TimoWey/Belimo_RoomUnit_ESP32-C3/3D-Design/Assembly_Top_View.png

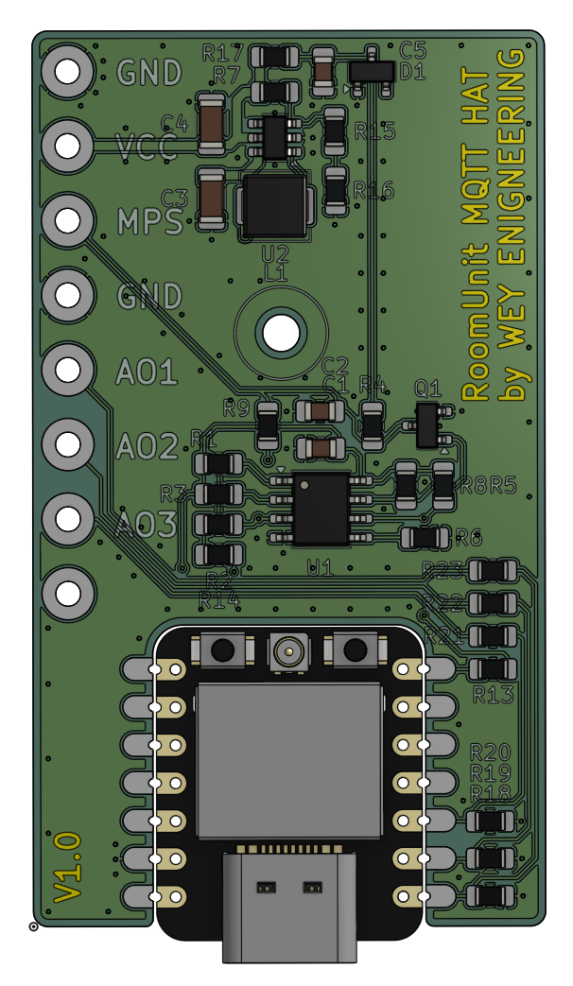
3D-Design/Assembly_Top_View.png
