TimoWey/Belimo_RoomUnit_ESP32-C3/3D-Design/Assembly_Side_View.png

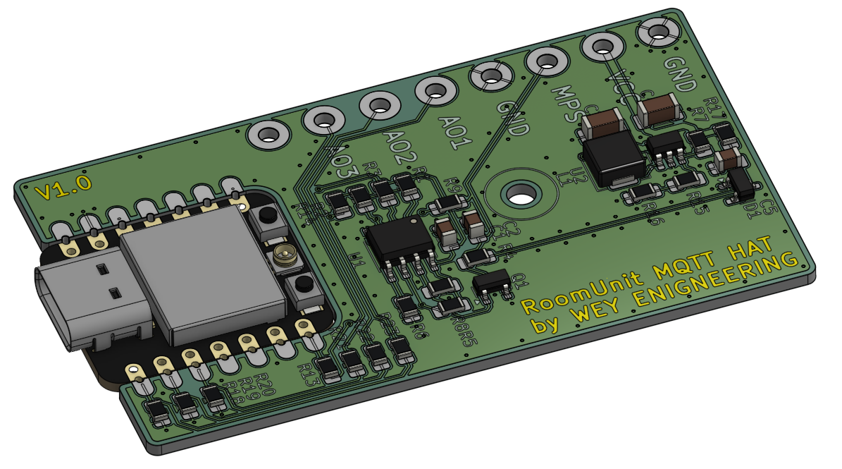
3D-Design/Assembly_Side_View.png
